peterisza/iec62386-wall-panel/firmware/source/uart.h

#ifndef UART_H
#define UART_H

#include <stdint.h>
#include <stdbool.h>

void uart_init(void);
void uart_send_string(const char* str);
void uart_send_char(char c);
void uart_send_hex_byte(uint8_t byte);
void uart_send_hex(const uint8_t* data, uint16_t len);
void uart_send_status_prefix(bool ok);
void uart_send_uint_dec(uint32_t value);
void uart_wait_for_tx_empty(void);

#endif // UART_H
